apatton090/KiCad/GettingToBlink5.0/GTB5_Pics/Design_Pics/back2.PNG

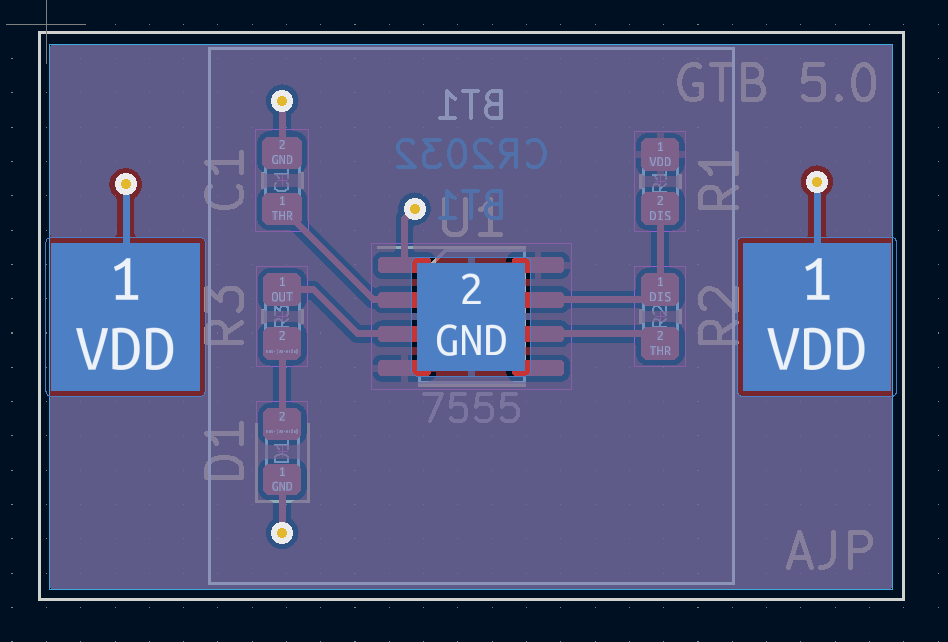
GettingToBlink5.0/GTB5_Pics/Design_Pics/back2.PNG
