apatton090/KiCad/GettingToBlink5.0/GTB5_Simulation/GTB5_Sim.asc

C1: cap; 1µ
D1: LED; QTLP690C
R1: res; 1k
R2: res; 470k
R3: res; 1k
U1: NE555
V1: voltage; 9
Named nets: 0, DIS, VCC, TRIG
.tran 0 10 0
